ednieuw/FourLanguageClock/4LanguageClock/4-talenklok_IMG_1176.jpg

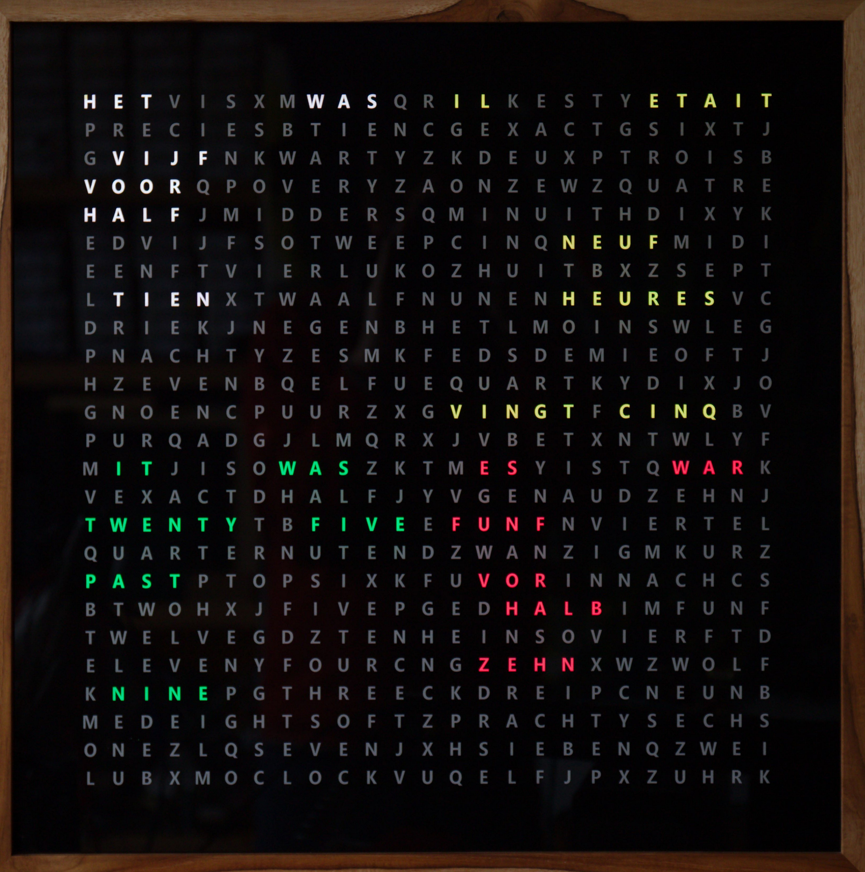
4LanguageClock/4-talenklok_IMG_1176.jpg
