ednieuw/FourLanguageClock/4LanguageClock/IMG_5557.JPG

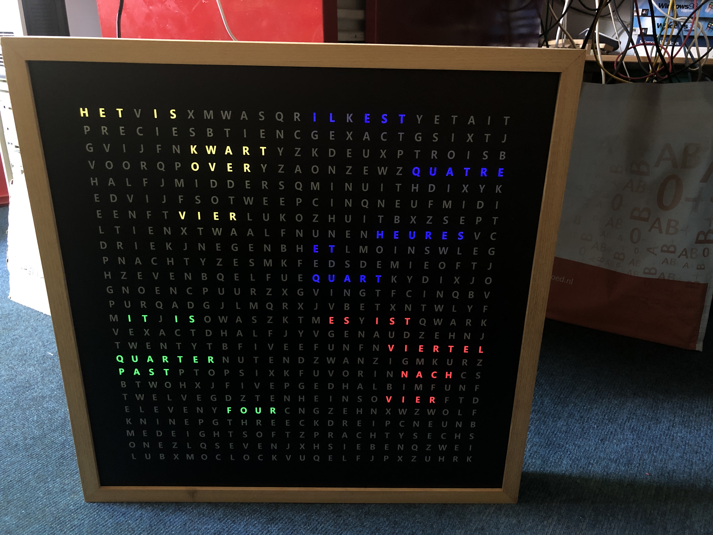
4LanguageClock/IMG_5557.JPG
