ednieuw/FourLanguageClock/4LanguageClock/IMG_5557k.JPG

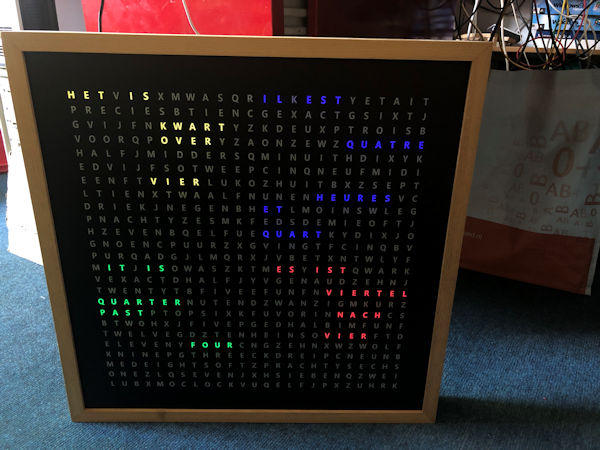
4LanguageClock/IMG_5557k.JPG
