ednieuw/FourLanguageClock/4LanguageClock/IMG_5560.JPG

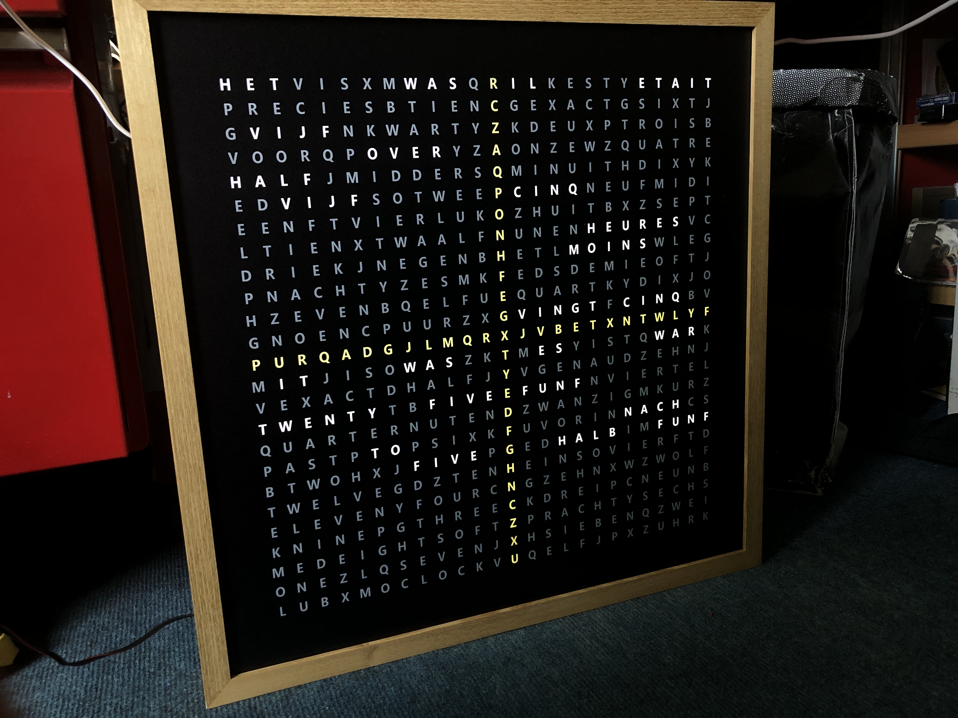
4LanguageClock/IMG_5560.JPG
