ednieuw/FourLanguageClock/Bouwpakketkleur_files/CIMG2972.JPG

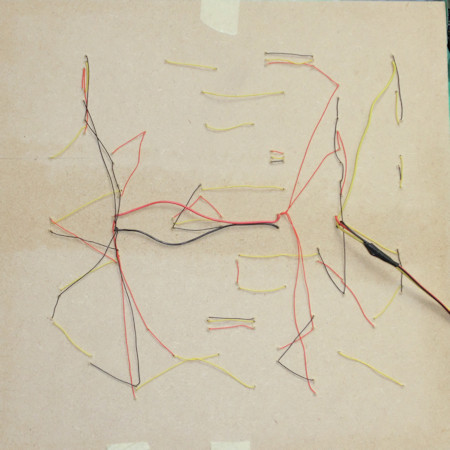
Bouwpakketkleur_files/CIMG2972.JPG
