ednieuw/FourLanguageClock/Bouwpakketkleur_files/CIMG3003.JPG

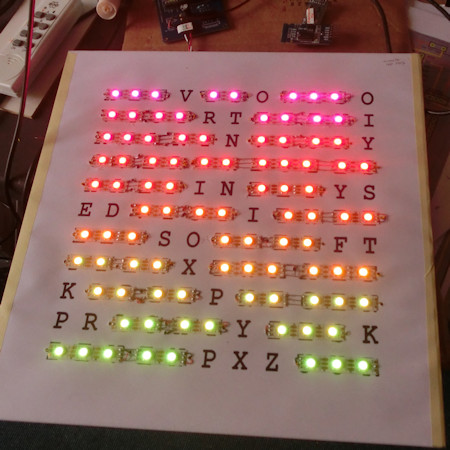
Bouwpakketkleur_files/CIMG3003.JPG
