ednieuw/FourLanguageClock/Bouwpakketkleur_files/Colour Word Clock PCBV08.jpg

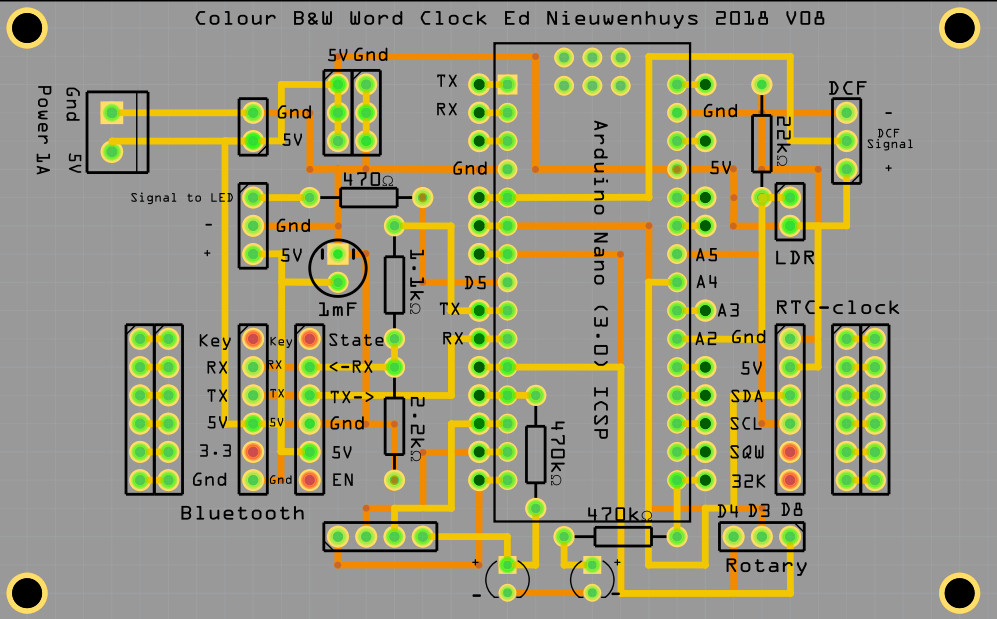
Bouwpakketkleur_files/Colour Word Clock PCBV08.jpg
