ednieuw/FourLanguageClock/Bouwpakketkleur_files/Colour Word Clock PCBV16.jpg

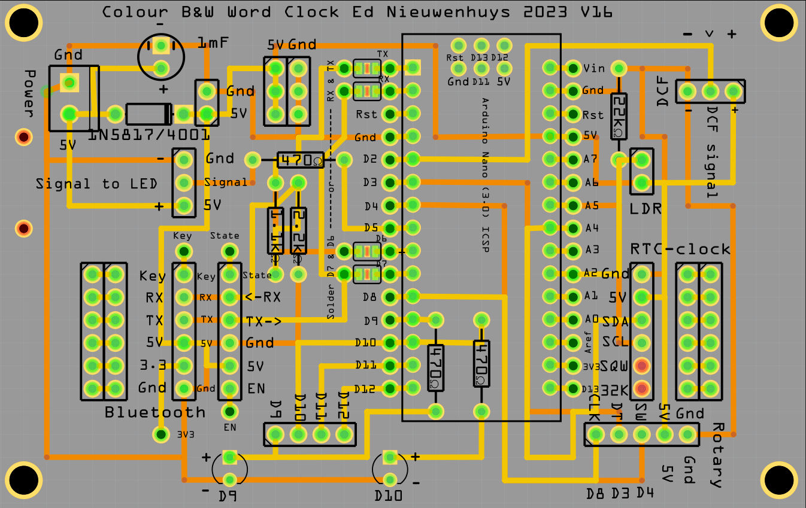
Bouwpakketkleur_files/Colour Word Clock PCBV16.jpg
