ednieuw/FourLanguageClock/Bouwpakketkleur_files/FibonacciklokPCBV05_pcb.jpg

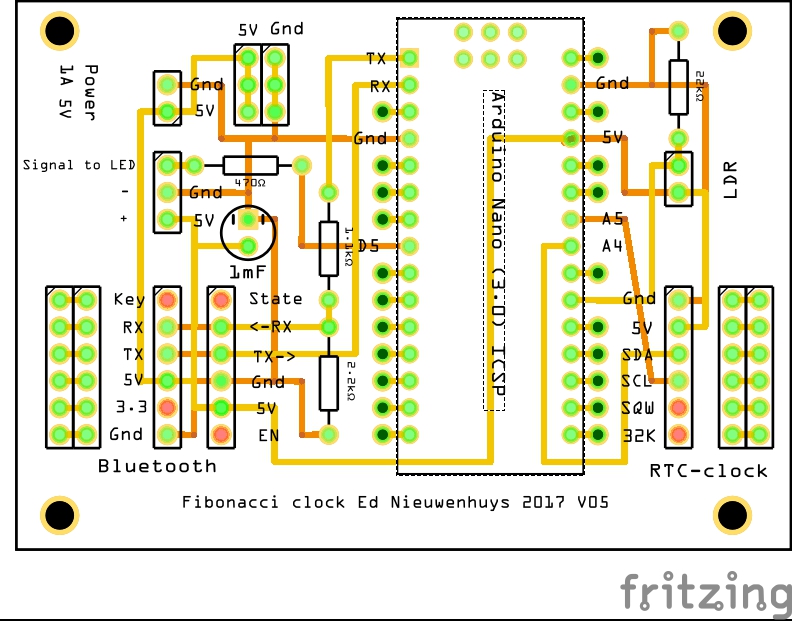
Bouwpakketkleur_files/FibonacciklokPCBV05_pcb.jpg
