ednieuw/FourLanguageClock/Bouwpakketkleur_files/IMG_6073.JPG

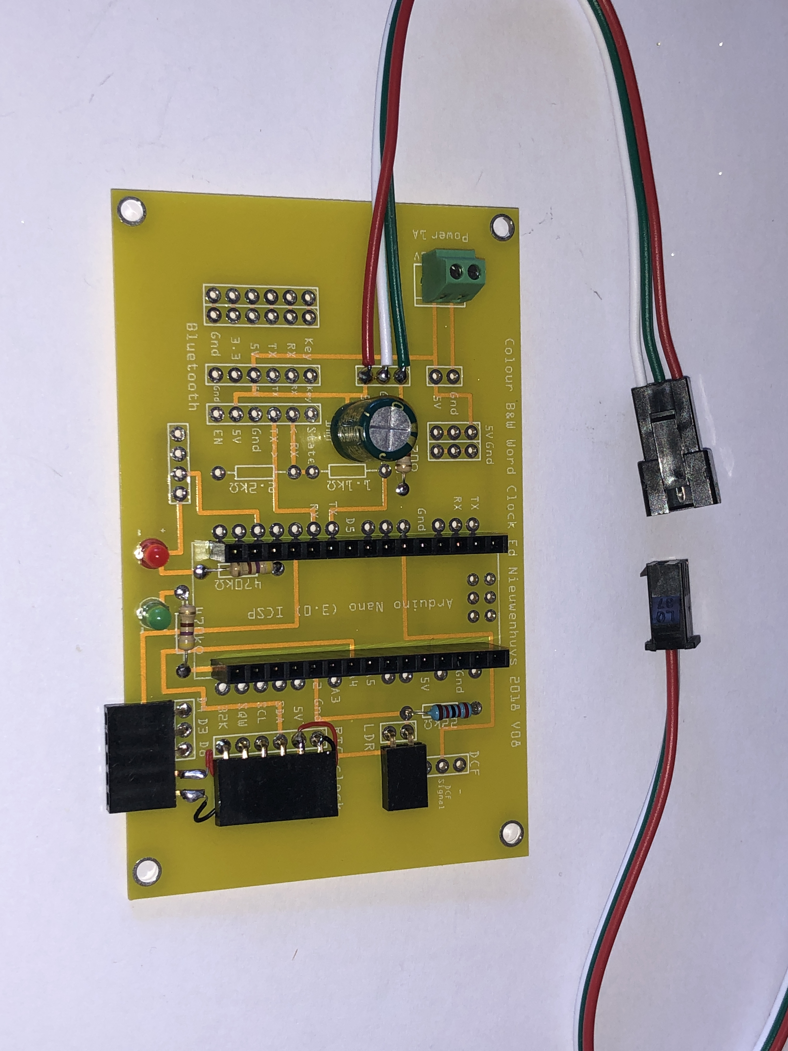
Bouwpakketkleur_files/IMG_6073.JPG
