ednieuw/FourLanguageClock/Bouwpakketkleur_files/InterieurCIMG1600.JPG

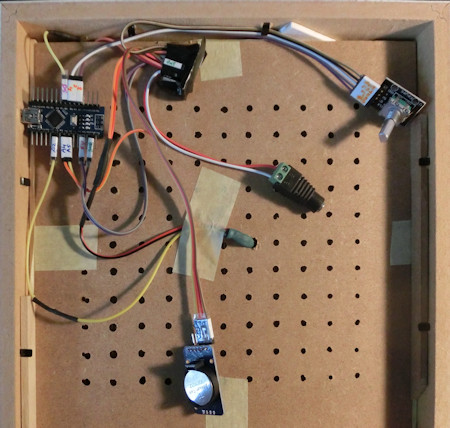
Bouwpakketkleur_files/InterieurCIMG1600.JPG
