ednieuw/FourLanguageClock/Bouwpakketkleur_files/InterieurNanoCIMG1600.JPG

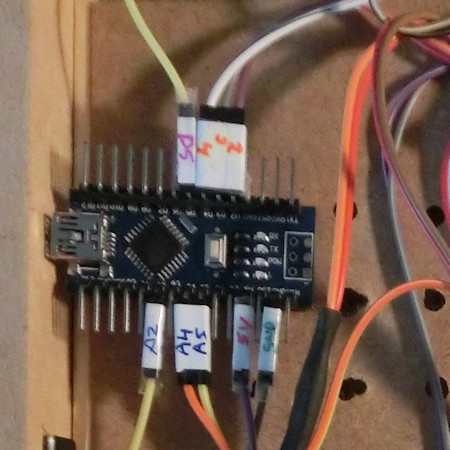
Bouwpakketkleur_files/InterieurNanoCIMG1600.JPG
