ednieuw/FourLanguageClock/Bouwpakketkleur_files/KleurenklokCIMG1645.JPG

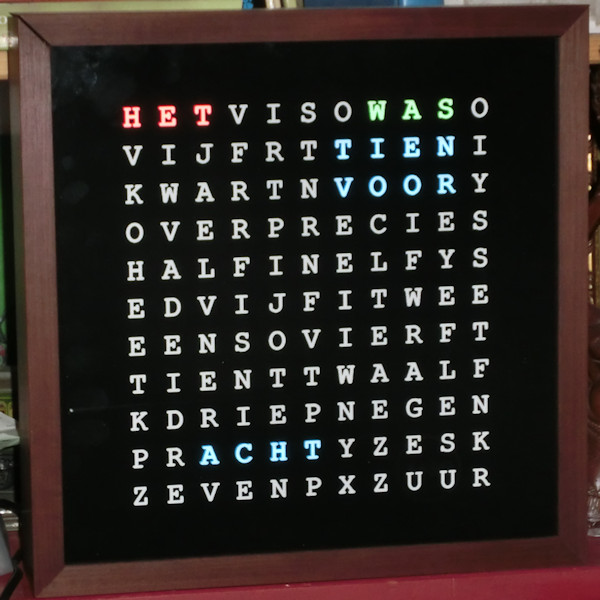
Bouwpakketkleur_files/KleurenklokCIMG1645.JPG
