ednieuw/FourLanguageClock/Bouwpakketkleur_files/KleurenklokCIMG16451.JPG

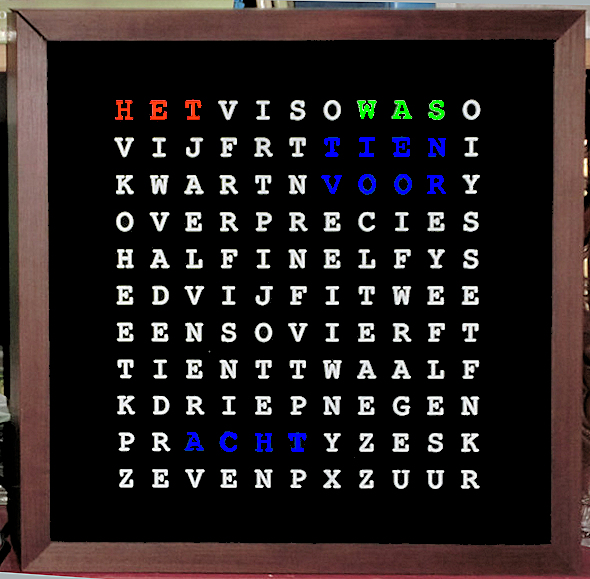
Bouwpakketkleur_files/KleurenklokCIMG16451.JPG
