ednieuw/FourLanguageClock/Bouwpakketkleur_files/PCBV08_IMG_6073.JPG

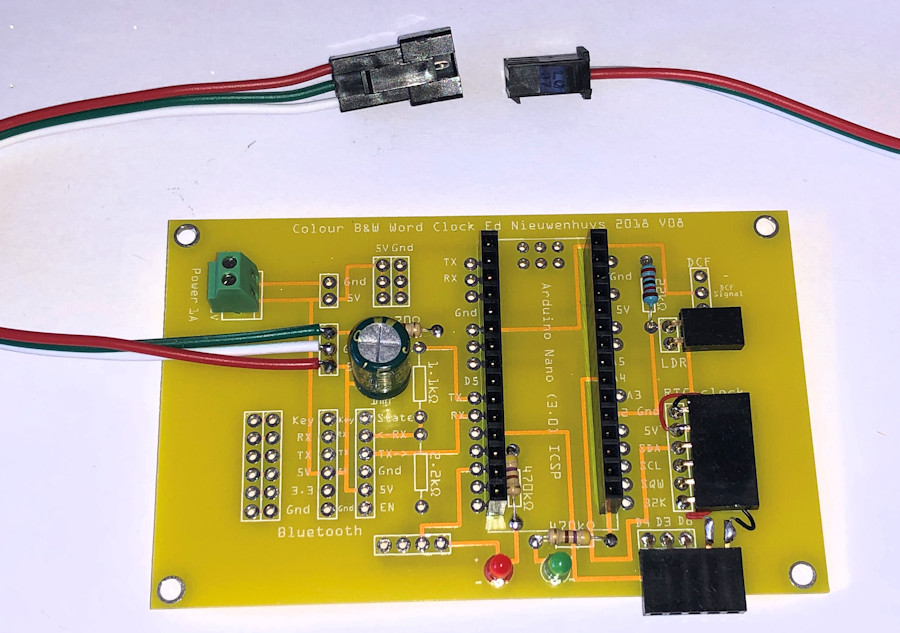
Bouwpakketkleur_files/PCBV08_IMG_6073.JPG
