ednieuw/FourLanguageClock/Bouwpakketkleur_files/WS2812CIMG2949.JPG

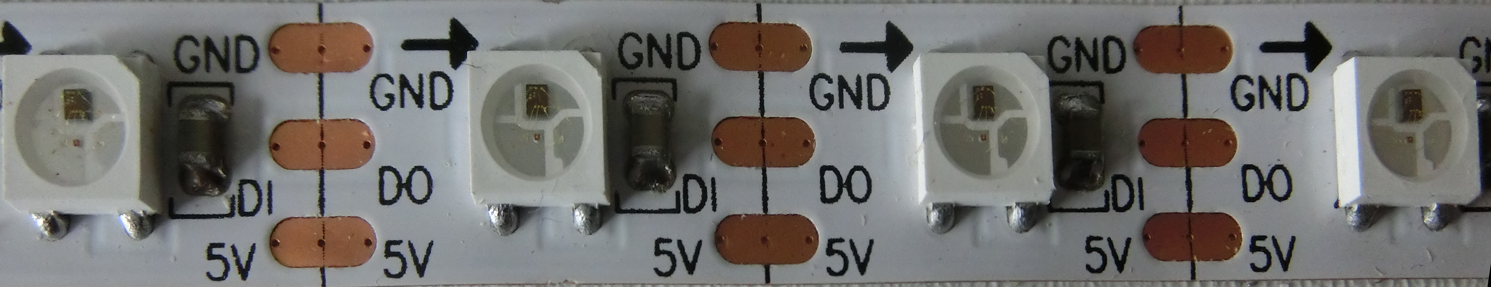
Bouwpakketkleur_files/WS2812CIMG2949.JPG
