ednieuw/FourLanguageClock/Bouwpakketkleur_files/WS2812detailCIMG2949.JPG

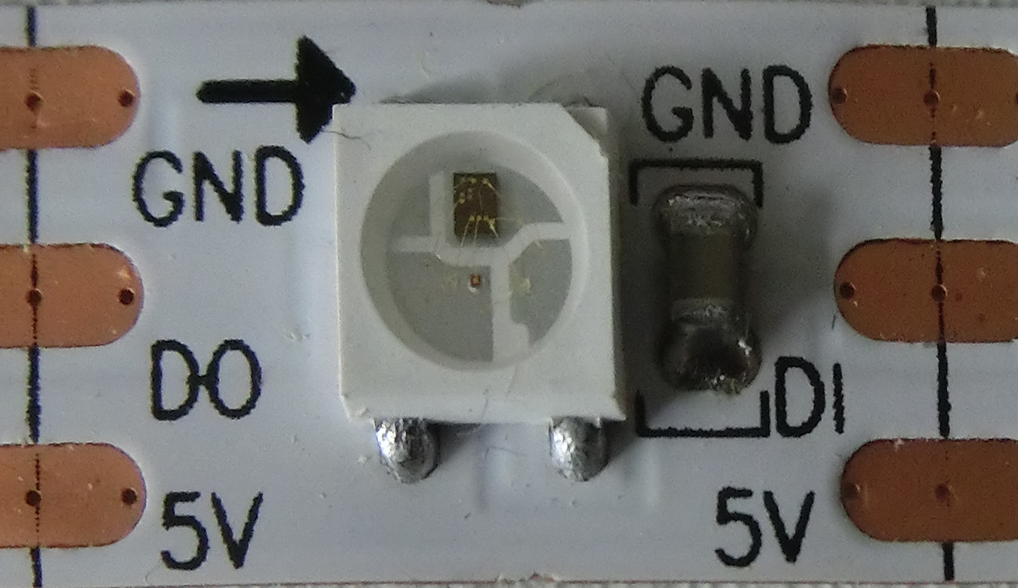
Bouwpakketkleur_files/WS2812detailCIMG2949.JPG
