ednieuw/FourLanguageClock/WoordklokSK6812_files/ColourWordClockPCBV14.jpg

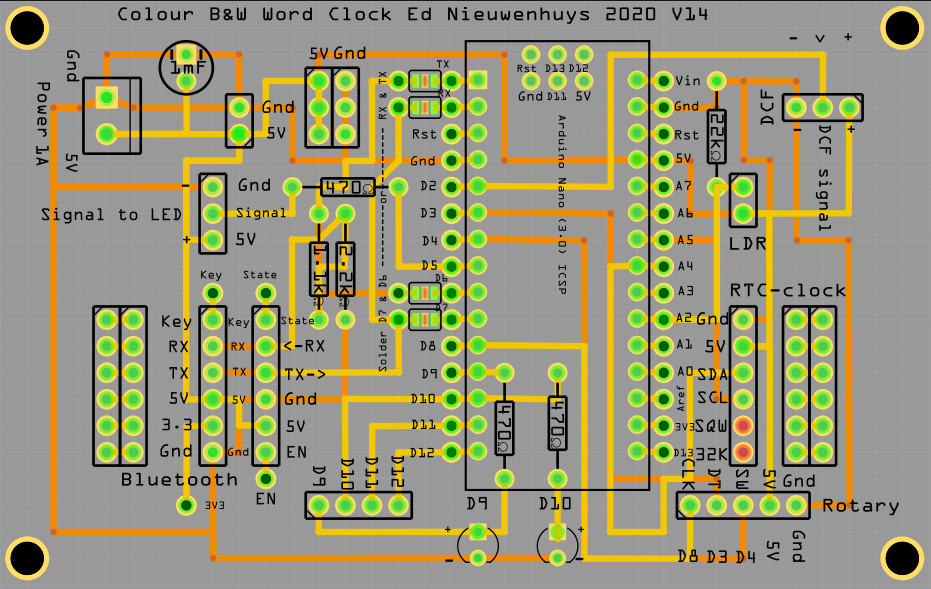
WoordklokSK6812_files/ColourWordClockPCBV14.jpg
