ednieuw/FourLanguageClock/WoordklokSK6812_files/ColourWordClockPCBV15.jpg

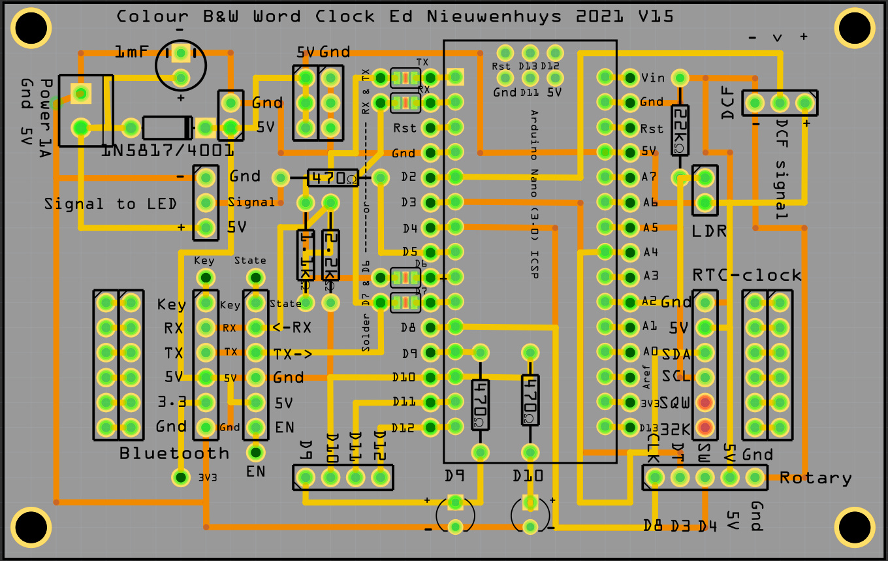
WoordklokSK6812_files/ColourWordClockPCBV15.jpg
