ednieuw/FourLanguageClock/WoordklokSK6812_files/IMG_1474.JPG

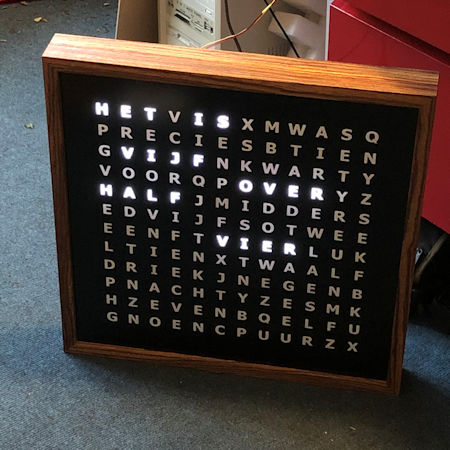
WoordklokSK6812_files/IMG_1474.JPG
