ednieuw/FourLanguageClock/WoordklokSK6812_files/IMG_1550.jpg

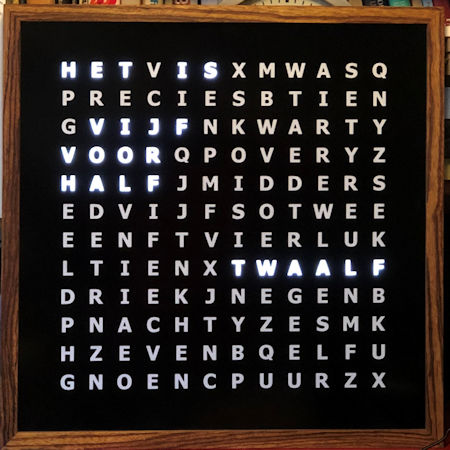
WoordklokSK6812_files/IMG_1550.jpg
