ednieuw/FourLanguageClock/WoordklokSK6812_files/IMG_2364.jpg

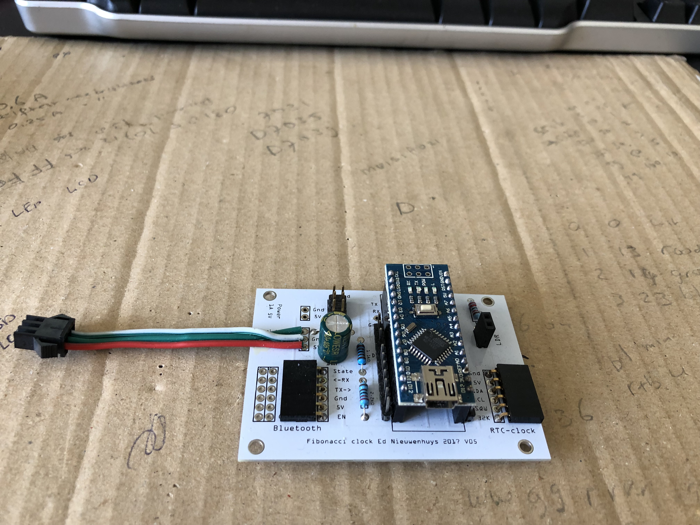
WoordklokSK6812_files/IMG_2364.jpg
