ednieuw/FourLanguageClock/WoordklokSK6812_files/IMG_5466.JPG

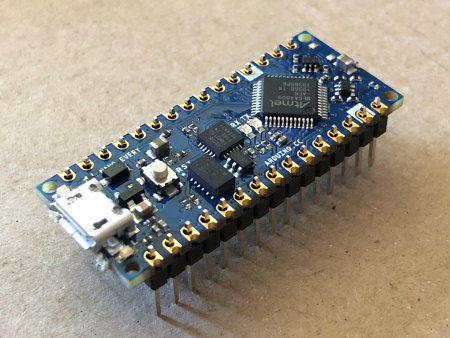
WoordklokSK6812_files/IMG_5466.JPG
