ednieuw/FourLanguageClock/WoordklokSK6812_files/IMG_5467.JPG

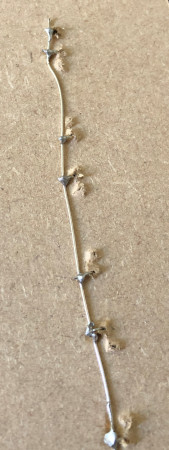
WoordklokSK6812_files/IMG_5467.JPG
