ednieuw/FourLanguageClock/WoordklokSK6812_files/klok-IMG_2305.jpg

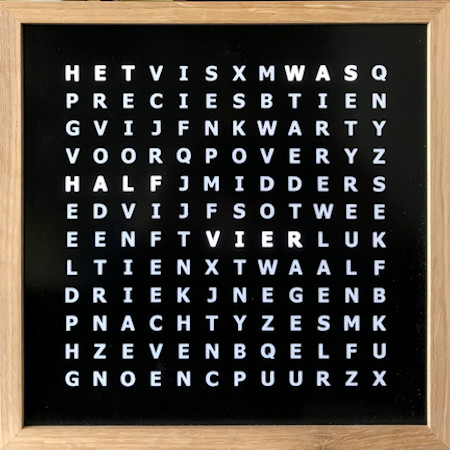
WoordklokSK6812_files/klok-IMG_2305.jpg
