ednieuw/FourLanguageClock/WoordklokSK6812_files/LEDs-op-plaatIMG_2296.jpg

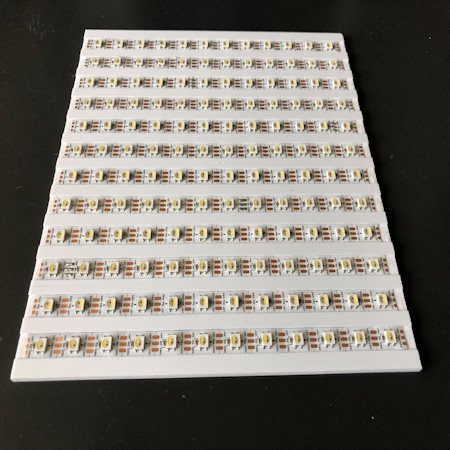
WoordklokSK6812_files/LEDs-op-plaatIMG_2296.jpg
