ednieuw/FourLanguageClock/WoordklokSK6812_files/Nederlands_08sep2018_50x50cm (2).jpg

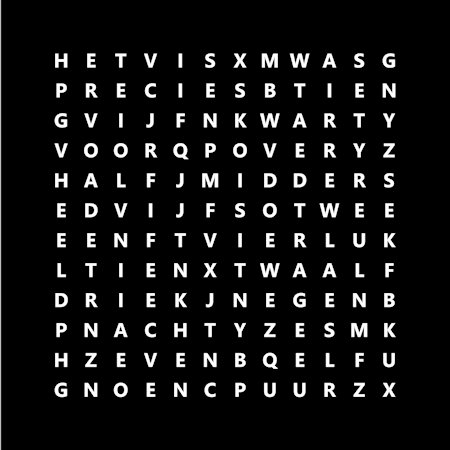
WoordklokSK6812_files/Nederlands_08sep2018_50x50cm (2).jpg
