ednieuw/FourLanguageClock/WoordklokSK6812_files/PCB-IMG_9407.JPG

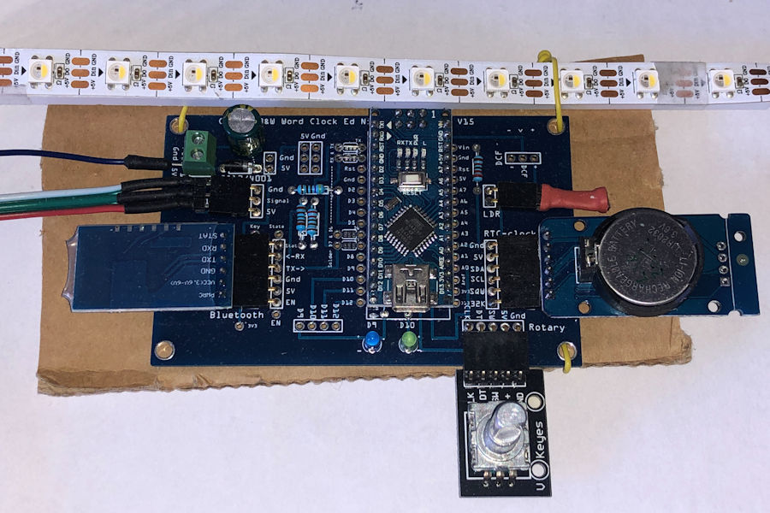
WoordklokSK6812_files/PCB-IMG_9407.JPG
